camswords/quadcopter/src/stm32f4/src/analytics.h

#ifndef ANALYTICS_H_
#define ANALYTICS_H_

#include <stdint.h>
#include <ring_buffer.h>

RingBuffer metricsRingBuffer;

void InitialiseAnalytics();

void RecordIntegerMetric(uint8_t type, uint8_t loopReference, uint32_t value);

void RecordFloatMetric(uint8_t type, uint8_t loopReference, float value);

void RecordPanicMessage(char *message);
void RecordWarningMessage(char *message);

void FlushMetrics();
void FlushAllMetrics();

#endif
