camswords/quadcopter/src/stm32f4/src/gyroscope.h

#ifndef GYROSCOPE_H_
#define GYROSCOPE_H_

#include <i2c.h>
#include <stdint.h>

bool isReadingGyroscope;

typedef struct GyroscopeReading {
	float x;
	float y;
	float z;
	float gyroscopeTemperature;
	float xOffset;
	float yOffset;
	float zOffset;
	uint32_t readings;
}GyroscopeReading;

struct GyroscopeReading gyroscopeReading;

void InitialiseGyroscope();

void ReadGyroscope();

#endif
