camswords/quadcopter/src/stm32f4/src/delay.c

//******************************************************************************

// https://my.st.com/public/STe2ecommunities/mcu/Lists/cortex_mx_stm32/Flat.aspx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

volatile unsigned int *DWT_CYCCNT   = (volatile unsigned int *)0xE0001004; //address of the register
volatile unsigned int *DWT_CONTROL  = (volatile unsigned int *)0xE0001000; //address of the register
volatile unsigned int *SCB_DEMCR        = (volatile unsigned int *)0xE000EDFC; //address of the register

//******************************************************************************

#include <delay.h>

void EnableTiming(void)
{
    static int enabled = 0;

    if (!enabled)
    {
        *SCB_DEMCR = *SCB_DEMCR | 0x01000000;
        *DWT_CYCCNT = 0; // reset the counter
        *DWT_CONTROL = *DWT_CONTROL | 1 ; // enable the counter

        enabled = 1;
    }
}

//******************************************************************************

void TimingDelay(unsigned int tick)
{
    unsigned int start, current;

    start = *DWT_CYCCNT;

    do
    {
        current = *DWT_CYCCNT;
    } while((current - start) < tick);
}

//******************************************************************************

void WaitASecond() {
	TimingDelay(160000000);
}

void WaitAMillisecond() {
	TimingDelay(160000);
}

void WaitAFewMillis(int16_t millis) {
	TimingDelay(160000000 / 1000 * millis);
}
